samitha278/5-Band-Equalizer/Images/Final/Demonstration.JPG

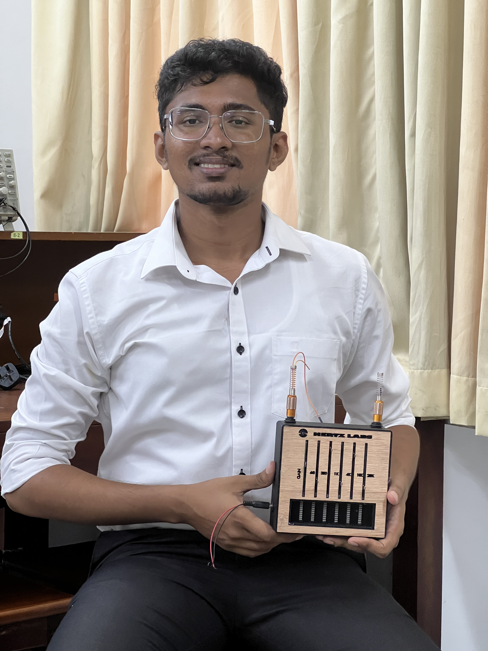
Images/Final/Demonstration.JPG
