samitha278/5-Band-Equalizer/Images/Design and Schematics/input.png

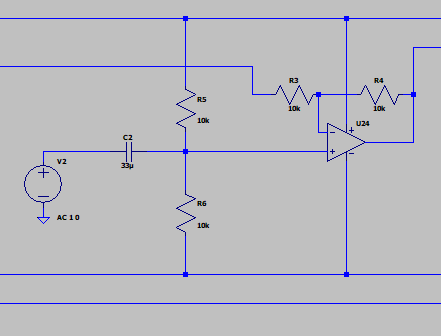
Images/Design and Schematics/input.png
