samitha278/5-Band-Equalizer/Images/Design and Schematics/LT_Spice_schematic.png

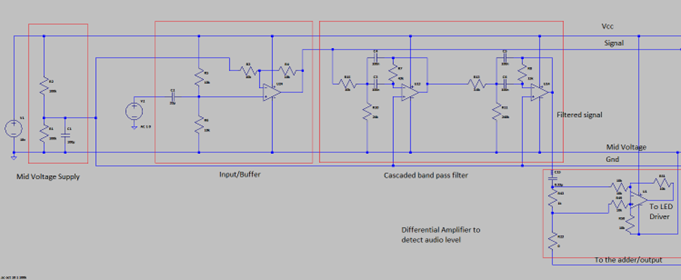
Images/Design and Schematics/LT_Spice_schematic.png
