samitha278/5-Band-Equalizer/Images/Design and Schematics/MFB_circuit.png

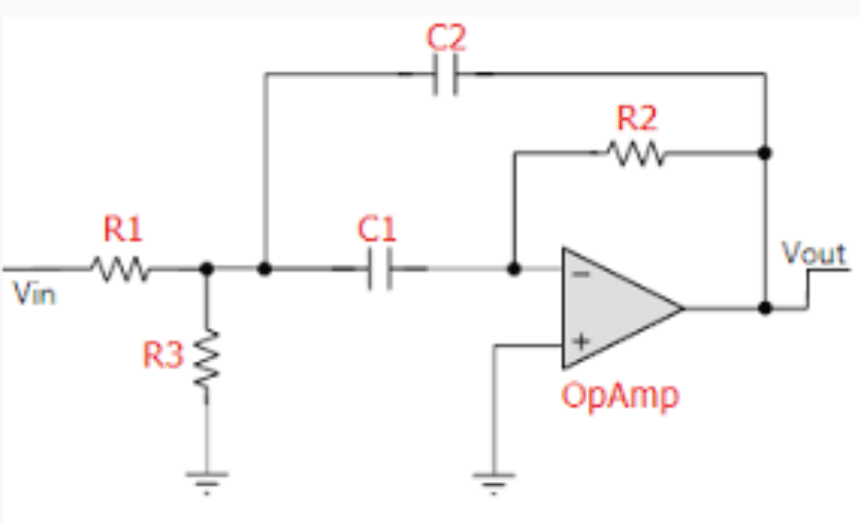
Images/Design and Schematics/MFB_circuit.png
