samitha278/5-Band-Equalizer/Images/Design and Schematics/response_1.png

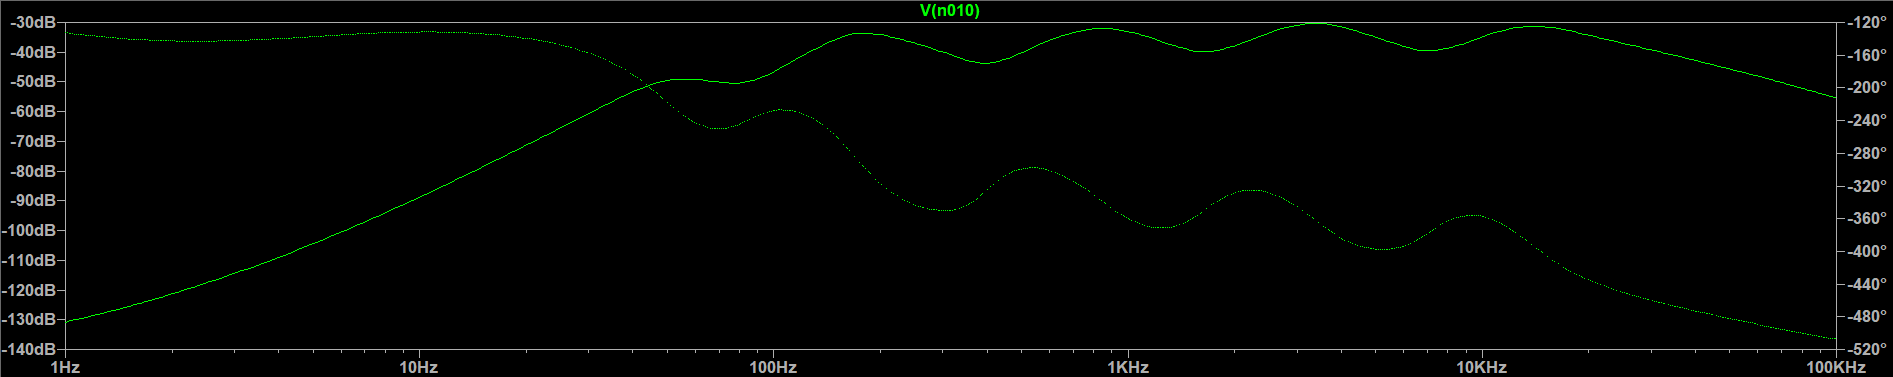
Images/Design and Schematics/response_1.png
