samitha278/5-Band-Equalizer/Images/Design and Schematics/Screenshot 2024-08-19 182646.png

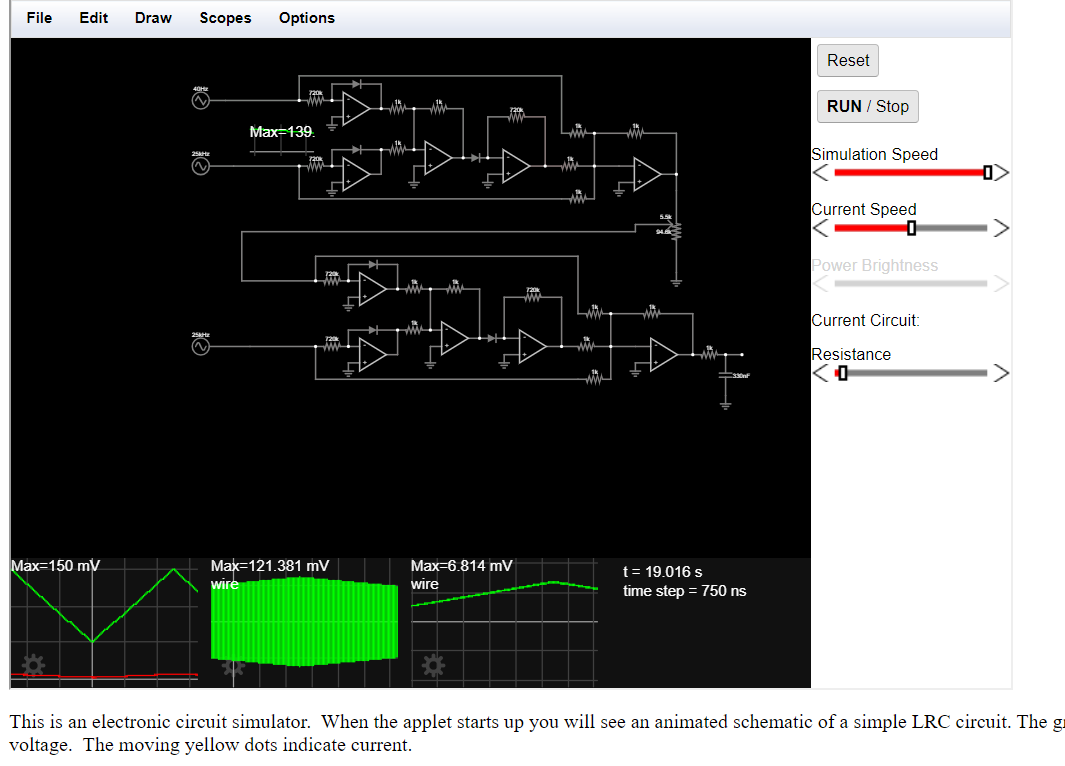
Images/Design and Schematics/Screenshot 2024-08-19 182646.png
