samitha278/5-Band-Equalizer/Images/Design and Schematics/simulation_response.png

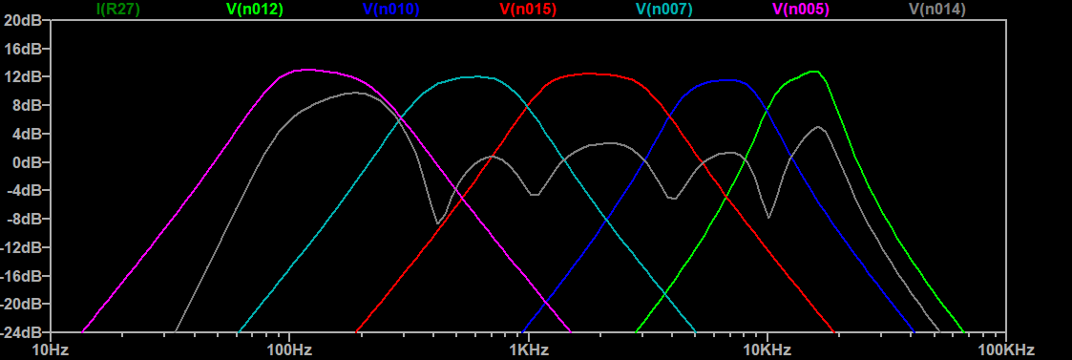
Images/Design and Schematics/simulation_response.png
