samitha278/5-Band-Equalizer/Images/Final/Equalizer PCB.JPG

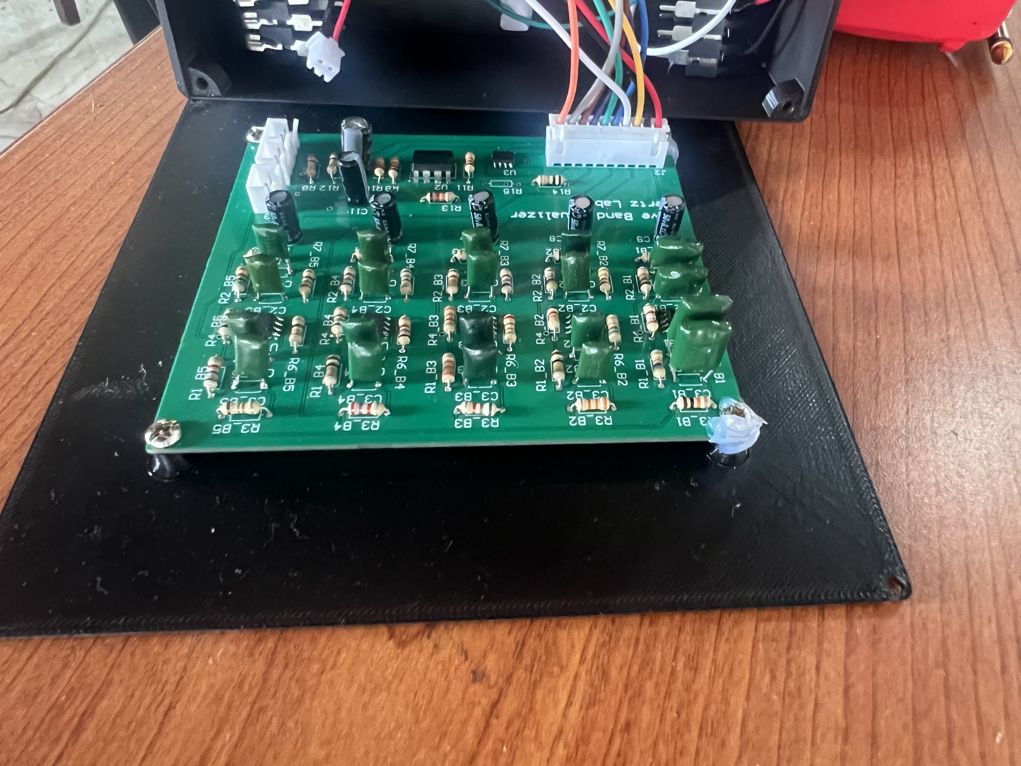
Images/Final/Equalizer PCB.JPG
