samitha278/5-Band-Equalizer/Images/Final/Team.JPG

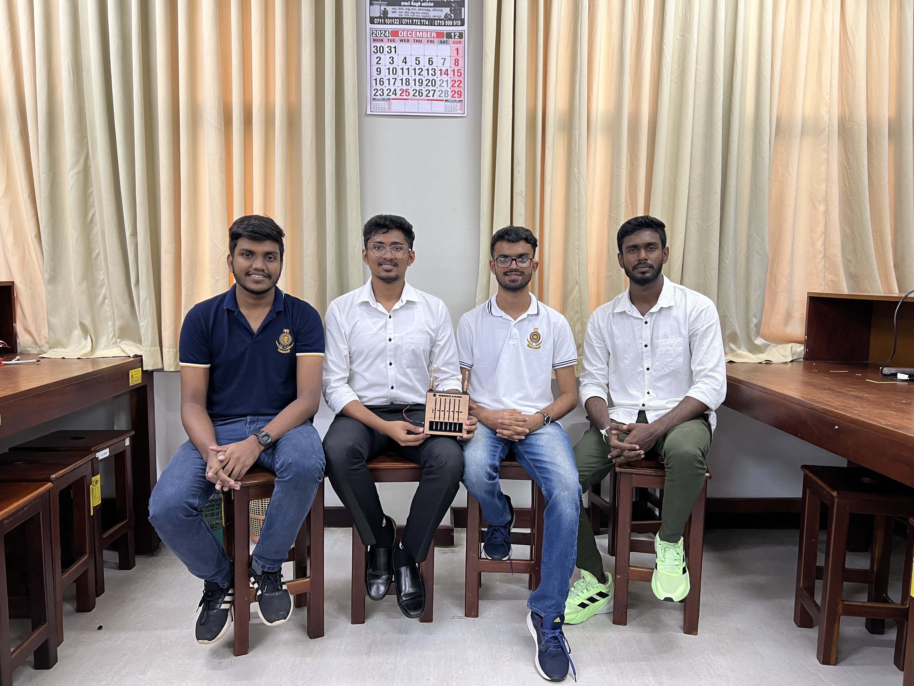
Images/Final/Team.JPG
