samitha278/5-Band-Equalizer/Simulation Files/Final_Advanced_Equilizer.asc

0.047u: cap; 10n
10k: res; 10k
C1: cap; 100µ
C2: cap; 33µ
C3: cap; 100n
C4: cap; 100n
C5: cap; 100n
C6: cap; 100n
C7: cap; 10n
C8: cap; 10n
C9: cap; 10n
C10: cap; 10n
C11: cap; 10n
C13: cap; 10n
C14: cap; 10n
C15: cap; 0.33µ
C16: cap; 10n
C17: cap; 0.1µ
C18: cap; 10n
C19: cap; 10n
C20: cap; 10n
C21: cap; 0.1µ
C22: cap; 10n
C23: cap; 10n
C24: cap; 10n
C25: cap; 10n
C26: cap; 0.1µ
C27: cap; 0.1µ
R1: res; 100k
R2: res; 100k
R3: res; 10k
R4: res; 10k
R5: res; 10k
R6: res; 10k
R7: res; 43k
R8: res; 15k
R9: res; 100k
R10: res; 24k
R11: res; 240k
R12: res; 56k
R13: res; 3.6k
R14: res; 27k
R15: res; 10k
R16: res; 51k
R17: res; 20k
R18: res; 12k
R19: res; 33k
R20: res; 22k
R21: res; 6.8k
R22: res; 11k
R23: res; 0
R24: res; 1.8k
R25: res; 5k
R26: res; 2.7k
R27: res; 2.5k
R28: res; 6.8k
R29: res; 13k
R30: res; 6.8k
R31: res; 3.3k
R32: res; 750
R33: res; 1.8k
R34: res; 5k
R35: res; 6.2k
R36: res; 430
R37: res; 1.5k
R38: res; 5.6k
R39: res; 180
R40: res; 1.3k
R41: res; 5k
R42: res; 5k
R43: res; 1k
R44: res; 1k
R45: res; 1k
R46: res; 1k
R47: res; 1k
R49: res; 10k
R50: res; 10k
R51: res; 10k
U1: UniversalOpAmp
U13: UniversalOpAmp
U14: UniversalOpAmp
U15: UniversalOpAmp
U16: UniversalOpAmp
U17: UniversalOpAmp
U18: UniversalOpAmp
U19: UniversalOpAmp
U20: UniversalOpAmp
U21: UniversalOpAmp
U22: UniversalOpAmp
U23: UniversalOpAmp
U24: UniversalOpAmp
V1: voltage; 18v
V2: voltage; ""; AC 1 0
Named nets: 0
.ac oct 10 1 100k
.tran 0 100ms 1ms 0.001ms
