samitha278/5-Band-Equalizer/Simulation Files/Simulations/Advanced_Equilizer.asc

0.047u: cap; 33n
C1: cap; 100µ
C2: cap; 33µ
C3: cap; 6.8n
C4: cap; 6.8n
C5: cap; 68n
C6: cap; 68n
C7: cap; 10n
C8: cap; 10n
C9: cap; 100n
C10: cap; 100n
C11: cap; 33n
C13: cap; 15n
C14: cap; 100n
C15: cap; 0.1µ
C16: cap; 15n
C17: cap; 0.1µ
C18: cap; 33n
C19: cap; 100n
C20: cap; 33n
C21: cap; 0.1µ
C22: cap; 1n
C23: cap; 1n
C24: cap; 1n
C25: cap; 1n
C26: cap; 0.1µ
C27: cap; 0.1µ
R1: res; 100k
R2: res; 100k
R3: res; 10k
R4: res; 10k
R5: res; 10k
R6: res; 10k
R7: res; 180k
R8: res; 47k
R9: res; 47k
R10: res; 68k
R11: res; 15k
R12: res; 1k
R13: res; 15k
R14: res; 1.5k
R15: res; 47k
R16: res; 12k
R17: res; 2.7k
R18: res; 3.3k
R19: res; 3.3k
R20: res; 680
R21: res; 1k
R22: res; 3.3k
R23: res; 10k
R24: res; 470
R25: res; 10k
R26: res; 1k
R27: res; 330k
R28: res; 3.3k
R29: res; 2.2k
R30: res; 680
R31: res; 1k
R32: res; 470
R33: res; 1k
R34: res; 10k
R35: res; 100k
R36: res; 1.5k
R37: res; 33k
R38: res; 100k
R39: res; 2.2k
R40: res; 33k
R41: res; 33k
R42: res; 10k
U13: UniversalOpAmp
U14: UniversalOpAmp
U15: UniversalOpAmp
U16: UniversalOpAmp
U17: UniversalOpAmp
U18: UniversalOpAmp
U19: UniversalOpAmp
U20: UniversalOpAmp
U21: UniversalOpAmp
U22: UniversalOpAmp
U23: UniversalOpAmp
U24: UniversalOpAmp
V1: voltage; 5v
V2: voltage; ""; AC 1 0
Named nets: 0
.ac oct 10 1 100k
