samitha278/5-Band-Equalizer/Simulation Files/Simulations/Calculated_Equilizer.asc

10n: cap; 10n
C1: cap; 100µ
C2: cap; 33µ
C3: cap; 100n
C4: cap; 100n
C5: cap; 100n
C6: cap; 100n
C7: cap; 100n
C8: cap; 100n
C9: cap; 100n
C10: cap; 100n
C11: cap; 10n
C13: cap; 10n
C14: cap; 10n
C15: cap; 0.22µ
C16: cap; 10n
C17: cap; 10µ
C18: cap; 10n
C19: cap; 10n
C20: cap; 10n
C21: cap; 10µ
C22: cap; 10n
C23: cap; 10n
C24: cap; 10n
C25: cap; 10n
C26: cap; 10µ
C27: cap; 10µ
R1: res; 100k
R2: res; 100k
R3: res; 10k
R4: res; 10k
R5: res; 10k
R6: res; 10k
R7: res; 47k
R8: res; 18k
R9: res; 12k
R10: res; 56k
R11: res; 22k
R12: res; 2.2k
R13: res; 3.9k
R14: res; 2.7k
R15: res; 10k
R16: res; 6.8k
R17: res; 1.2k
R18: res; 1.5k
R19: res; 33k
R20: res; 10k
R21: res; 6.8k
R22: res; 15k
R23: res; 1K
R24: res; 1.2k
R25: res; 5k
R26: res; 3.3k
R27: res; 5K
R28: res; 8.2k
R29: res; 18k
R30: res; 6.8k
R31: res; 3.9k
R32: res; 680
R33: res; 1.8k
R34: res; 5k
R35: res; 8.2k
R36: res; 330
R37: res; 1.8k
R38: res; 5.6k
R39: res; 220
R40: res; 1.2k
R41: res; 5k
R42: res; 7.5k
R43: res; 33K
U13: UniversalOpAmp
U14: UniversalOpAmp
U15: UniversalOpAmp
U16: UniversalOpAmp
U17: UniversalOpAmp
U18: UniversalOpAmp
U19: UniversalOpAmp
U20: UniversalOpAmp
U21: UniversalOpAmp
U22: UniversalOpAmp
U23: UniversalOpAmp
U24: UniversalOpAmp
V1: voltage; 16
V2: voltage; ""; AC 1 0
Named nets: 0
.ac oct 10 1 100k
