samitha278/5-Band-Equalizer/Simulation Files/Simulations/Equilizer.asc

C1: cap; 100µ
C2: cap; 33µ
C3: cap; 0.1µ
C4: cap; 0.1µ
C5: cap; 0.1µ
C6: cap; 0.1µ
C7: cap; 0.047µ
C8: cap; 0.047µ
C9: cap; 0.0022µ
C10: cap; 0.0022µ
C11: cap; 0.0022µ
C12: cap; 0.0022µ
C13: cap; 0.1µ
C15: cap; 0.1µ
C16: cap; 0.1µ
C17: cap; 0.1µ
C18: cap; 0.1µ
R1: res; 10k
R2: res; 10k
R3: res; 10k
R4: res; 10k
R5: res; 10k
R6: res; 10k
R7: res; 82k
R8: res; 13k
R9: res; 6.2k
R10: res; 27k
R11: res; 6.3k
R12: res; 3.3k
R13: res; 6.8k
R14: res; 2.7k
R15: res; 12k
R16: res; 30k
R17: res; 18k
R18: res; 15k
R19: res; 9.1k
R20: res; 43k
R21: res; 3.3k
R22: res; 10k
R23: res; 10k
R24: res; 1k
R25: res; 10k
R26: res; 10k
R27: res; 330k
R28: res; 1k
U1: OP227
U2: OP227
U3: OP227
U4: OP227
U5: OP227
U6: OP227
U7: OP227
V1: voltage; 9v
V2: voltage; ""; AC 1 0
Named nets: 0
.ac oct 10 1 100k
