samitha278/5-Band-Equalizer/Images/Final/5 Band Visualizing.JPG

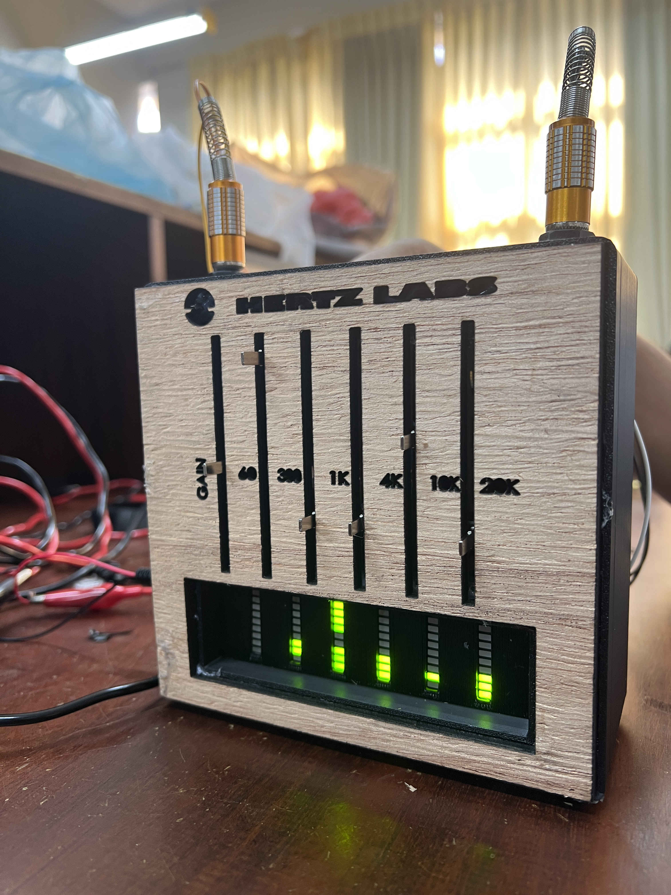
Images/Final/5 Band Visualizing.JPG
