samitha278/5-Band-Equalizer/Images/Final/Final Product.JPG

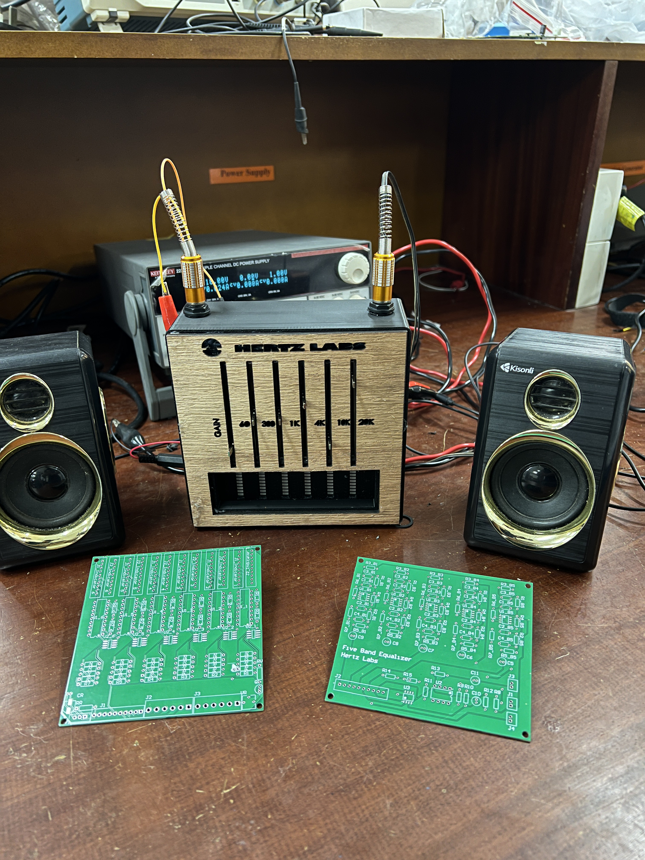
Images/Final/Final Product.JPG
